LuizGuimah/LineFollower-GERM-RISO/media/photo_1.jpg

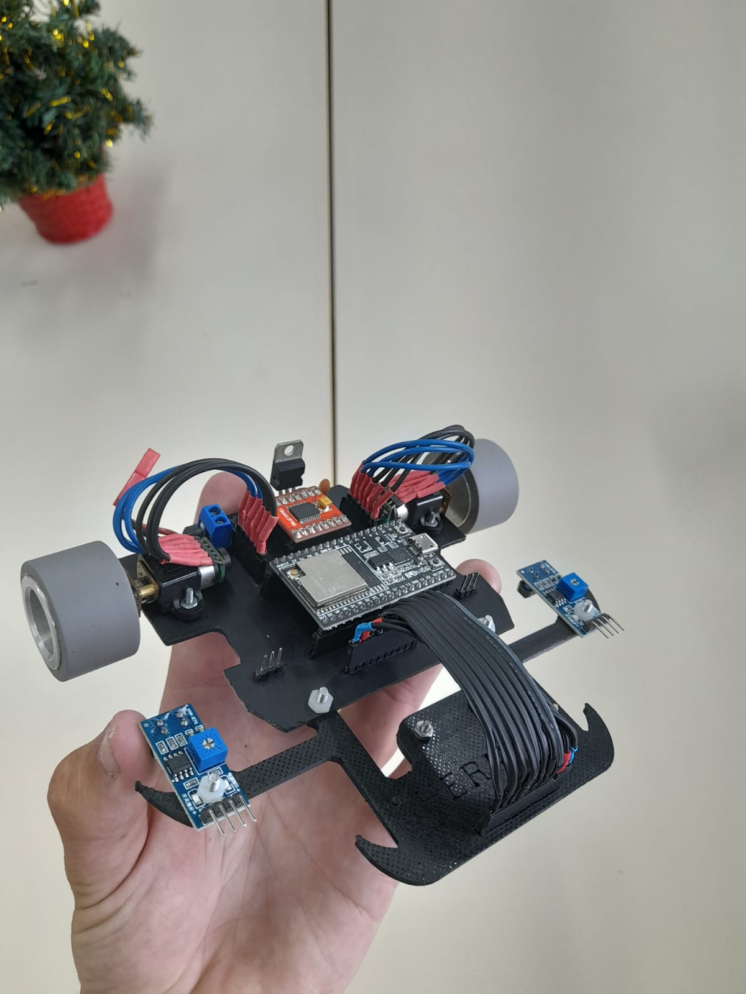
media/photo_1.jpg
