LuizGuimah/LineFollower-GERM-RISO/media/photo_2.jpg

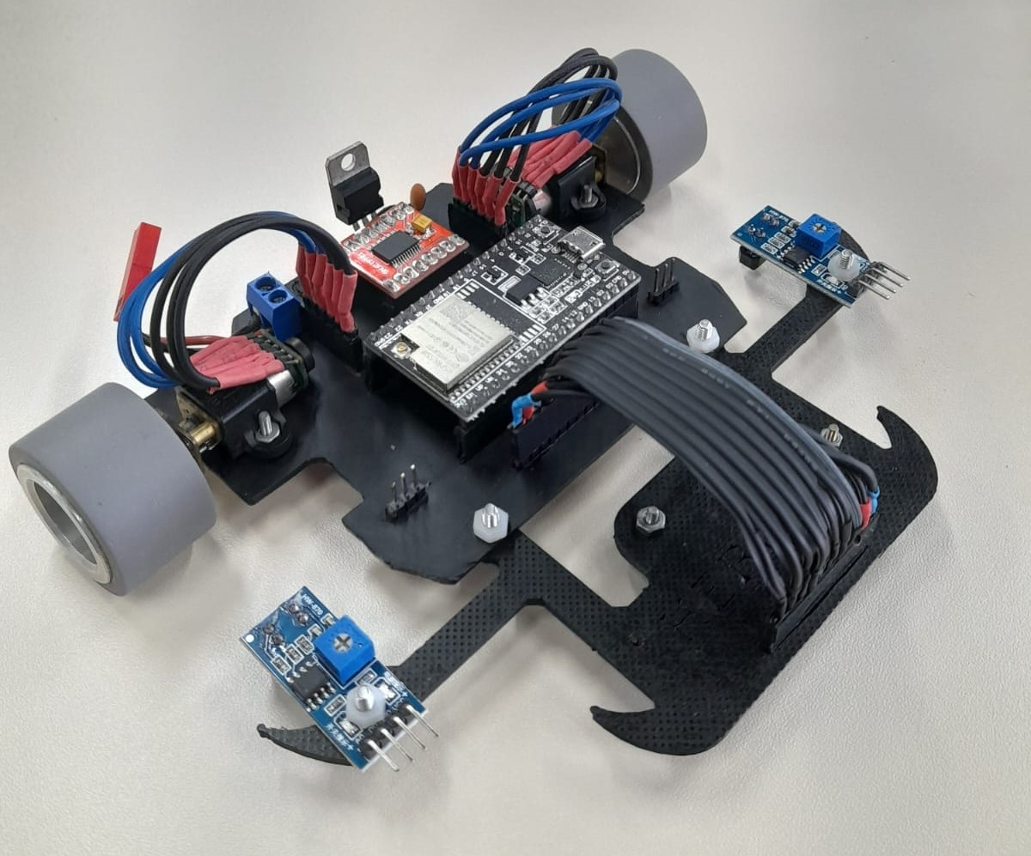
media/photo_2.jpg
