LuizGuimah/LineFollower-GERM-RISO/media/photo_3.jpg

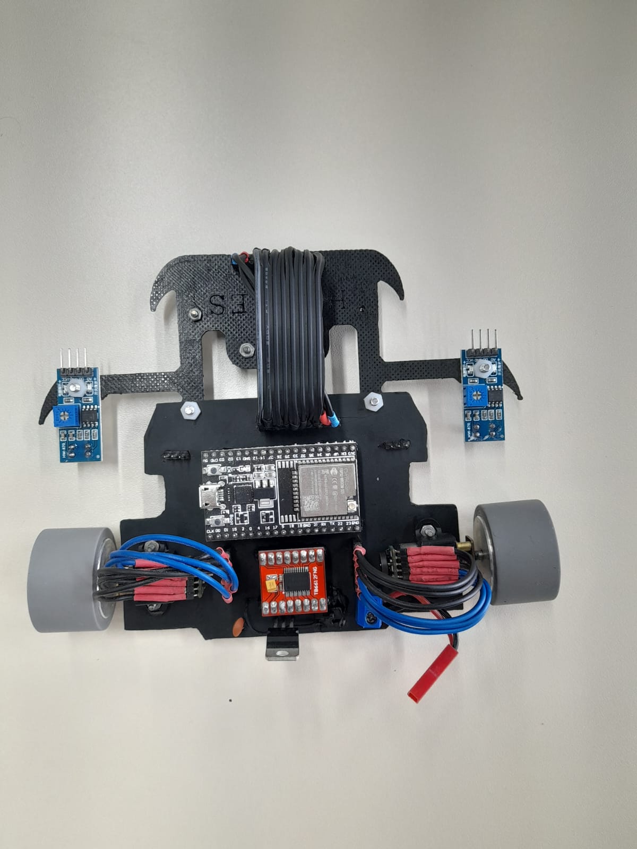
media/photo_3.jpg
